JPZV/OpenPico64/sw/openpico64/openpico64_pins.h

/**
 * SPDX-License-Identifier: BSD-2-Clause
 *
 * Copyright (c) 2022 Konrad Beckmann
 * Copyright (c) 2026 JPZV
 */

#pragma once


#define SD_MISO         ( 0)

#define N64_COLD_RESET  ( 1)

#define SD_CLK          ( 2)
#define SD_MOSI         ( 3)

#define N64_AD0         ( 4)
#define N64_AD1         ( 5)
#define N64_AD2         ( 6)
#define N64_AD3         ( 7)
#define N64_AD4         ( 8)
#define N64_AD5         ( 9)
#define N64_AD6         (10)
#define N64_AD7         (11)
#define N64_AD8         (12)
#define N64_AD9         (13)
#define N64_AD10        (14)
#define N64_AD11        (15)
#define N64_AD12        (16)
#define N64_AD13        (17)
#define N64_AD14        (18)
#define N64_AD15        (19)

#define N64_WRITE       (20)
#define N64_READ        (21)

#define N64_ALEL        (22)
#define N64_ALEH        (26)
